partlyhuman/loopycart/labels/Lupirom-1200dpi.png

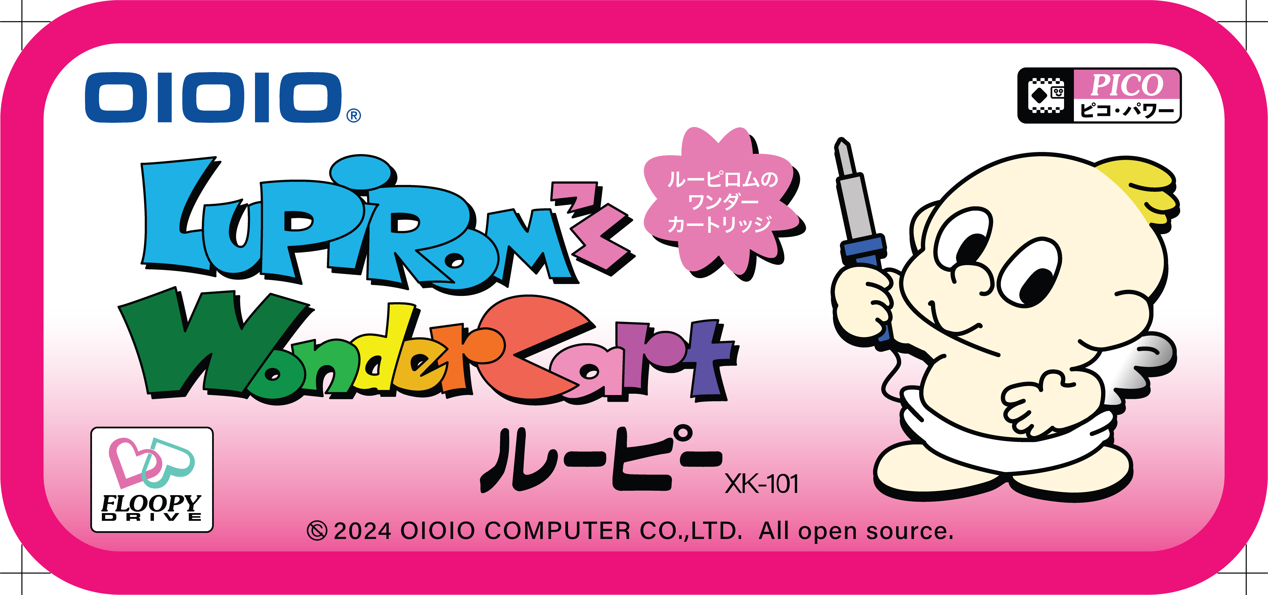
labels/Lupirom-1200dpi.png
