partlyhuman/loopycart/flash-programmer/pico/zmain.ino

static bool PROGRAM_DEBUGGING = false;

// When the cart is inserted into a Loopy, the ~INSERTED pin gets grounded
// We then switch to a serial forwarding loop
void onInserted() {
  bool isInserted = digitalRead(PIN_INSERTED) == LOW;
  if (PROGRAM_DEBUGGING != isInserted) {
    ledColor(0x80ff80);
    rp2040.reboot();
  }
}

void loop() {
  if (PROGRAM_DEBUGGING) {
    loop_debugging();
  } else {
    loop_programming();
  }
}

void setup() {
  led.begin();

  // Externally pulled up, active/inserted low
  pinMode(PIN_INSERTED, INPUT);
  PROGRAM_DEBUGGING = digitalRead(PIN_INSERTED) == LOW;

  attachInterrupt(digitalPinToInterrupt(PIN_INSERTED), onInserted, CHANGE);

  if (PROGRAM_DEBUGGING) {
    setup_debugging();
  } else {
    setup_programming();
  }
}
