partlyhuman/loopycart/flash-programmer/pico/flash.ino

// Make sure the BE1 don't keep getting twiddled back and forth,
// use 0 as a command address BUT KEEP BE1 SET
inline uint32_t zeroWithBank(uint32_t addr) {
  return addr & FLASH_BANK_SIZE;
}

// Bus states - Sharp flash uses 3 wire control and these are predefined states

inline void busRead() {
  setControl(ROMCE & OE);
  databusReadMode();
}

inline void busWrite() {
  setControl(ROMCE & ROMWE);
  databusWriteMode();
}

inline void busIdle() {
  setControl(IDLE);
  databusWriteMode();
}

// The two basic building blocks: read a word, and send a command / write a word

uint16_t flashReadWord(uint32_t addr) {
  busIdle();

  setAddress(addr);

  busRead();

  // tAVQV | Address to output delay | MAX 100ns
  NOP;
  NOP;
  NOP;
  NOP;
  NOP;
  NOP;
  NOP;
  NOP;
  NOP;
  NOP;
  NOP;
  NOP;
  NOP;
  NOP;
  NOP;

  uint16_t data = readWord();
  busIdle();

  // tAVAV | Read Cycle Time | MIN 120ns
  NOP;
  NOP;
  NOP;

  return data;
}

void flashCommand(uint32_t addr, uint16_t data) {
  busIdle();

  // tEHEL | BE# Pulse Width High | Min 25ns
  // This will easily be accomplished during the following writeWord.
  NOP;
  NOP;
  NOP;
  NOP;

  writeWord(addr, data);

  busWrite();

  // tELEH | BE# Pulse Width | Min 70ns
  NOP;
  NOP;
  NOP;
  NOP;
  NOP;
  NOP;
  NOP;
  NOP;
  NOP;
  NOP;

  busIdle();
}

void flashReadStatus() {
  busRead();
  NOP;
  NOP;
  NOP;
  NOP;
  NOP;
  NOP;
  SRD = readByte();
  busIdle();
}

// returns TRUE if OK
bool flashStatusCheck(uint32_t addr = 0, bool clearIfError = true) {
  bool ok = true;
  flashCommand(zeroWithBank(addr), 0x70);
  flashReadStatus();
  if (!SR(7)) {
    echo_all("STATUS busy\r\n");
    ok = false;
  }
  if (SR(5) && SR(4)) {
    echo_all("STATUS improper command\r\n");
    ok = false;
  }
  if (SR(3)) {
    echo_all("STATUS undervoltage\r\n");
    ok = false;
  }
  if (SR(1)) {
    echo_all("STATUS locked\r\n");
    ok = false;
  }
  if (SR(2)) {
    echo_all("STATUS write suspended\r\n");
    ok = false;
  }
  if (SR(6)) {
    echo_all("STATUS erase suspended\r\n");
    ok = false;
  }
  if (!ok && clearIfError) {
    // clear status register
    flashCommand(0, 0x50);
  }
  return ok;
}

void flashWaitUntilIdle(uint us = 10) {
  do {
    delayMicroseconds(us);
    flashReadStatus();
  } while (!SR(7));
}

// Major functions

void flashEraseBank(int bank) {
  int32_t bankAddress = bank ? FLASH_BANK_SIZE : 0;
  sprintf(S, "Erase bank %d\r", bank);
  echo_all();

  delayMicroseconds(100);
  flashCommand(bankAddress, 0x70);
  flashWaitUntilIdle();
  delayMicroseconds(100);

  delayMicroseconds(100);
  flashCommand(bankAddress, 0x30);
  delayMicroseconds(100);
  flashCommand(bankAddress, 0xd0);

  const int TIMEOUT_MS = 30000;
  const int CHECK_INTERVAL_MS = 1000;
  for (int time = 0; time < TIMEOUT_MS; time += CHECK_INTERVAL_MS) {
    flashReadStatus();
    if (SR(7)) {
      echo_all("DONE!\r");
      break;
    } else {
      echo_all(".");
      delay(CHECK_INTERVAL_MS);
    }
  }

  if (flashStatusCheck(bankAddress)) {
    echo_all("Bank erase successful!\r");
  }

  // if (SR(4) == 1 && SR(5) == 1) {
  //   echo_all("Invalid Bank Erase command sequence\r");
  // } else if (SR(5) == 1) {
  //   echo_all("Bank Erase error\r");
  // } else {
  //   echo_all("Bank Erase successful!\r");
  // }

  // clear status register
  flashCommand(0, 0x50);
  delayMicroseconds(100);
  // Read mode
  flashCommand(0, 0xff);
  delayMicroseconds(100);
}

void flashEraseAll() {
  stopwatch = millis();
  flashEraseBank(0);
  flashEraseBank(1);
  sprintf(S, "Erased in %0.2fs\r\n", (millis() - stopwatch) / 1000.0);
  echo_all();
}

bool flashEraseBlock(uint32_t startAddr) {
  //startAddr = startAddr & ~(FLASH_BLOCK_SIZE - 1);
  // sprintf(S, "Erase block %06xh-%06xh\r\n", startAddr, startAddr + FLASH_BLOCK_SIZE - 1);
  // echo_all();

  flashCommand(startAddr, 0x20);
  flashCommand(startAddr, 0xd0);
  flashWaitUntilIdle();

  return flashStatusCheck();
}

void flashClearLocks() {
  flashCommand(0, 0x60);
  flashCommand(0, 0xd0);
  flashWaitUntilIdle();

  if (flashStatusCheck()) {
    echo_all("Lock bits cleared successfully\r");
  }
}

// This should display the manufacturer and device code of the FLASH CHIP: B0 D0
void flashChipId() {
  busIdle();
  delayMicroseconds(100);

  flashCommand(0, 0x90);
  delayMicroseconds(100);

  busRead();
  delayMicroseconds(100);

  uint16_t manufacturer = flashReadWord(0);

  busIdle();
  delayMicroseconds(100);

  delay(100);
  uint16_t device = flashReadWord(2);

  databusWriteMode();
  flashCommand(0, CMD_RESET);
  delay(100);

  sprintf(S, "Manufacturer=%x Device=%x\r", manufacturer, device);
  echo_all();
}

// Does the cart start with 0E00 0080 like a loopy cart?
bool flashCartHeaderCheck() {
  return (flashReadWord(0x0) == 0x0e00 && flashReadWord(0x2) == 0x0080);
}

// What's the internal CRC32 in the cart header? Use this as a cart ID.
uint32_t flashCartHeaderId() {
  return (flashReadWord(0x8) << 16) | flashReadWord(0xA);
}

uint32_t flashCartHeaderSramSize() {
  uint32_t sramStart = (flashReadWord(0x10) << 16 | flashReadWord(0x12));
  uint32_t sramEnd = (flashReadWord(0x14) << 16 | flashReadWord(0x16));
  return sramEnd - sramStart + 1;
}

void flashInspect(uint32_t starting, uint32_t upto) {
  flashCommand(zeroWithBank(starting), 0xff);
  delayMicroseconds(1);

  for (uint32_t addr = starting; addr < upto; addr += 2) {
    if (addr % 0x10 == 0) {
      sprintf(S, "\r%06xh\t\t", addr);
      echo_all();
    }
    sprintf(S, "%04x\t", flashReadWord(addr));
    echo_all();
  }
}

void flashDump(uint32_t starting = 0, uint32_t upto = FLASH_SIZE) {
  uint32_t bank = ~0;

  for (uint32_t addr = starting; addr < upto; addr += 2) {
    uint32_t newBank = zeroWithBank(addr);
    if (bank != newBank) {
      bank = newBank;
      flashCommand(bank, CMD_RESET);
      delay(10);
    }
    uint16_t word = flashReadWord(addr);
    usb_web.write(word >> 8);
    usb_web.write(word & 0xff);
  }
  usb_web.flush();
}

// Returns whether programming should continue
bool flashWriteBuffer(uint8_t *buf, size_t bufLen, uint32_t &addr, uint32_t expectedBytes) {
  ledColor(0x400040);  // magenta

  if ((bufLen % 2) == 1) {
    sprintf(S, "WARNING: odd number of bytes %d\r", bufLen);
    echo_all();
  }

  if (bufLen <= 0) {
    echo_all("WARNING: Empty buffer\r");
  }

  // echo progress at fixed intervals
  // if (addr % 0x10000 == 0) {
  if (addr % 0x08000 == 0) {
    sprintf(S, "%06xh ", addr);
    echo_all();
  }

  // All of these are in BYTES
  // addr - overall address
  // buf - multi-byte buffer sent over by USB
  // bufLen - length of it
  // bufPtr - step through buffer using this

  // Multi-word write can write up to 32 bytes / 16 words
  const uint32_t bankBoundary = FLASH_BANK_SIZE;
  const size_t MAX_MULTIBYTE_WRITE = 32;
  bool atBoundary = false;
  uint32_t currentBank = zeroWithBank(addr);

  // Do however many multibyte writes necessary to empty the buffer
  for (int bufPtr = 0; bufPtr < bufLen;) {

    // Skip blocks of 0xff *between* multibyte writes only, assuming flash has been erased
    if (bufPtr + 1 < bufLen && buf[bufPtr] == buf[bufPtr + 1] == 0xff) {
      bufPtr += 2;
      addr += 2;
      continue;
    }

    int bytesToWrite = MIN(bufLen - bufPtr, MAX_MULTIBYTE_WRITE);
    // Don't allow multibyte writes to cross banks
    if (addr < bankBoundary && addr + bytesToWrite >= bankBoundary) {
      atBoundary = true;
      bytesToWrite = MIN(bankBoundary - addr, MAX_MULTIBYTE_WRITE);
      // sprintf(S, "\r\nFinal write into bank 0 writing %d bytes from %x to %x\r\n", bytesToWrite, addr, addr + bytesToWrite);
      // echo_all();
    }
    int wordsToWrite = bytesToWrite / 2;

    // Check status until we're ready to write more
    uint retries = 0;
    do {
      flashCommand(addr, 0xe8);
      flashReadStatus();

      if (SR(7)) {
        // READY
        break;
      } else {
        if (++retries > 1000) {
          sprintf(S, "\r\nTIMEOUT @ %06x\r\n", addr);
          echo_all();
          ledColor(RED);
          HALT;
        }
        // delayMicroseconds(10);
        continue;
      }

      // for bigger errors, have a bigger delay before retry
      if (SR(1) == SR(4) == 1) {
        sprintf(S, "Block lock error @ %06x\r\n", addr);
        echo_all();
      }
      if (SR(3) == SR(4) == 1) {
        sprintf(S, "Undervoltage error @ %06x\r\n", addr);
        echo_all();
      }
      if (SR(4) == 1 || SR(5) == 1) {
        sprintf(S, "Unable to multibyte write @ %06x\r\n", addr);
        echo_all();
      }
      delay(10);
    } while (!SR(7));

    // XSR.7 == 1 now, ready for write
    // A word/byte count (N)-1 is written with write address.
    flashCommand(addr, wordsToWrite - 1);

    // On the next write, device start address is written with buffer data.
    // Subsequent writes provide additional device address and data, depending on the count.
    // All subsequent address must lie within the start address plus the count.
    for (int j = 0; j < wordsToWrite; j++, addr += 2, bufPtr += 2) {
      uint16_t word = buf[bufPtr] << 8 | buf[bufPtr + 1];
      flashCommand(addr, word);
    }

    // After the final buffer data is written, write confirm (DOH) must be written.
    // This initiates WSM to begin copying the buffer data to the Flash Array.
    // Use the bank we started with not the bank we ended with
    flashCommand(currentBank, 0xd0);

    if (atBoundary) {
      do {
        delay(100);
      } while (!flashStatusCheck(currentBank));
      // clear status register
      flashCommand(0, 0x50);
      flashCommand(bankBoundary, CMD_RESET);
      flashCommand(bankBoundary, 0x50);
      // sprintf(S, "\rNew block bufPtr=%04x bufLen=%04x addr=%06x end=%06x\r", bufPtr, bufLen, addr, expectedBytes);
      // echo_all();
    }
  }

  if (addr >= expectedBytes) {
    delay(100);
    flashStatusCheck(addr, false);
    flashCommand(zeroWithBank(addr), CMD_RESET);
    flashCommand(zeroWithBank(addr), 0x50);

    sprintf(S, "\r\nWrote %d bytes in %0.2f sec using multibyte programming\r", addr * 2, (millis() - stopwatch) / 1000.0);
    echo_all();
    return false;
  }

  ledColor(0x101010);

  return true;
}
