partlyhuman/loopycart/flash-programmer/pico/sram.ino

#define SRAM_ADDRBITS 17  // R7 graduated to 1MBit/128KB SRAM
const uint32_t SRAM_SIZE = 1 << SRAM_ADDRBITS;

uint8_t sramReadByte(uint32_t addr) {
  setControl(RAMCE & OE);
  databusReadMode();

  // braindead 1 cycle read (address controlled)
  setAddress(addr);
  // tAA | Address access time | 55ns
  NOP;
  NOP;
  NOP;
  NOP;
  NOP;
  NOP;
  NOP;
  NOP;

  return readByte();
}

void sramWriteByte(uint32_t addr, uint8_t byte) {
  setControl(RAMCE);
  // Write Cycle 1, Note 4, p6 - During this period, I/O pins are in the output state, and input signals must not be applied.
  databusReadMode();

  setAddress(addr);
  NOP;
  NOP;
  NOP;

  setControl(RAMCE & RAMWE);
  NOP;
  NOP;
  NOP;

  databusWriteMode();
  mcpData.setPort(byte, A);

  setControl(RAMCE);
}

void sramSaveFile(const char* filename, uint32_t saveSize = SRAM_SIZE) {
  File file = LittleFS.open(filename, "w");

  // Address controlled Read Cycle 1, p5, no control necessary just set an address and read
  for (uint32_t addr = 0; addr < saveSize; addr++) {
    uint8_t byte = sramReadByte(addr);
    file.write(&byte, 1);
  }

  file.flush();
  file.close();
}

bool sramLoadFile(const char* filename) {
  if (!LittleFS.exists(filename)) {
    sprintf(S, "file %s doesn't exist\r\n", filename);
    echo_all();
    return false;
  }
  File file = LittleFS.open(filename, "r");
  auto fileSize = file.size();
  auto expectedFileSize = flashCartHeaderSramSize();
  if (fileSize > SRAM_SIZE) {
    sprintf(S, "Backed up file is bigger than SRAM size, aborting");
    LittleFS.remove(filename);
    return false;
  }
  if (fileSize != expectedFileSize) {
    sprintf(S, "Backup size %s is wrong size, expected %d, actual %d, continuing anyway...\r\n", filename, expectedFileSize, fileSize);
    echo_all();
  }

  // read 1kb at a time?
  const size_t CHUNK_SIZE = 1 << 10;
  uint8_t buf[CHUNK_SIZE];
  for (uint32_t addr = 0; addr < fileSize;) {
    // file.read() will do this for you if not enough available i guess
    // size_t bufSize = MIN(CHUNK_SIZE, SRAM_SIZE - addr);
    size_t bufSize = file.read(buf, CHUNK_SIZE);
    if (bufSize <= 0) break;
    for (size_t bufPtr = 0; bufPtr < bufSize; bufPtr++, addr++) {
      sramWriteByte(addr, buf[bufPtr]);
    }
  }

  file.close();
  return true;
}


void sramInspect(uint32_t starting = 0, uint32_t upto = SRAM_SIZE) {
  // Address controlled Read Cycle 1, p5, no control necessary just set an address and read
  for (uint32_t addr = starting; addr < upto; addr++) {
    if (addr % 0x10 == 0) {
      sprintf(S, "\r%06xh\t\t", addr);
      echo_all();
    }
    sprintf(S, "%02x\t", sramReadByte(addr));
    echo_all();
  }
}

void sramDump(uint32_t starting = 0, uint32_t upto = SRAM_SIZE) {
  // Address controlled Read Cycle 1, p5, no control necessary just set an address and read
  for (uint32_t addr = starting; addr < upto; addr++) {
    uint8_t byte = sramReadByte(addr);
    usb_web.write(&byte, 1);
  }
}

bool sramErase(uint32_t upto = SRAM_SIZE) {
  if (upto == SRAM_SIZE) {
    echo_all("Full erase SRAM");
  } else {
    sprintf(S, "Erasing SRAM up to %06xh", upto);
    echo_all();
  }

  stopwatch = millis();

  for (uint32_t addr = 0; addr < upto; addr++) {
    if (addr % 0x100 == 0) {
      echo_all(".");
    }
    sramWriteByte(addr, 0xff);
  }

  sprintf(S, "\r\nErased %d bytes of SRAM in %0.2f sec!\r\n", upto, (millis() - stopwatch) / 1000.0);
  echo_all();
  return true;
}

// Returns whether programming should continue
bool sramWriteBuffer(uint8_t* buf, size_t bufLen, uint32_t& addr, uint32_t expectedBytes) {
  for (int bufPtr = 0; bufPtr < bufLen && addr < expectedBytes; bufPtr++, addr++) {
    sramWriteByte(addr, buf[bufPtr]);
    // echo progress at fixed intervals
    if ((addr & 0x1fff) == 0) {
      sprintf(S, "%06xh ", addr);
      echo_all();
    }
  }

  if (addr >= expectedBytes) {
    sprintf(S, "\r\nWrote %d bytes in %0.2f sec\r\n", addr, (millis() - stopwatch) / 1000.0);
    echo_all();
    return false;
  }
  return true;
}
